leoo-c1/FPGA-Ethernet-FFT/rtl/fifo/audio_fifo_inst.v

audio_fifo	audio_fifo_inst (
	.aclr ( aclr_sig ),
	.data ( data_sig ),
	.rdclk ( rdclk_sig ),
	.rdreq ( rdreq_sig ),
	.wrclk ( wrclk_sig ),
	.wrreq ( wrreq_sig ),
	.q ( q_sig ),
	.rdempty ( rdempty_sig ),
	.rdusedw ( rdusedw_sig ),
	.wrfull ( wrfull_sig )
	);
