leoo-c1/FPGA-Ethernet-FFT/rtl/ram/amplitude_ram_inst.v

amplitude_ram	amplitude_ram_inst (
	.data ( data_sig ),
	.rdaddress ( rdaddress_sig ),
	.rdclock ( rdclock_sig ),
	.wraddress ( wraddress_sig ),
	.wrclock ( wrclock_sig ),
	.wren ( wren_sig ),
	.q ( q_sig )
	);
