leoo-c1/FPGA-Ethernet-FFT/rtl/fft/audio_fft/simulation/submodules/aldec/asj_fft_cnt_ctrl.vhd

-- (C) 2001-2025 Altera Corporation. All rights reserved.
-- This simulation model contains highly confidential and
-- proprietary information of Altera and is being provided
-- in accordance with and subject to the protections of the
-- applicable Altera Program License Subscription Agreement
-- which governs its use and disclosure. Your use of Altera
-- Corporation's design tools, logic functions and other
-- software and tools, and its AMPP partner logic functions,
-- and any output files from any of the foregoing (including device
-- programming or simulation files), and any associated
-- documentation or information are expressly subject to the
-- terms and conditions of the Altera Program License Subscription
-- Agreement, Altera IP License Agreement, or other
-- applicable license agreement, including, without limitation,
-- that your use is for the sole purpose of simulating designs
-- for use exclusively in logic devices manufactured by Altera and sold
-- by Altera or its authorized distributors. Please refer to the
-- applicable agreement for further details. Altera products and
-- services are protected under numerous U.S. and foreign patents,
-- maskwork rights, copyrights and other intellectual property laws.
-- Altera assumes no responsibility or liability arising out of the
-- application or use of this simulation model.
-- ACDS 25.1
`protect begin_protected
`protect version = 1
`protect encrypt_agent= "Aldec protectip", encrypt_agent_info= "Riviera-PRO 2019.10.138"
`protect key_keyowner= "Aldec", key_keyname= "ALDEC15_001", key_method= "rsa"
`protect encoding= (enctype="base64", line_length= 76, bytes= 256)
`protect key_block
D6r/H3scLRJbsmm2tHHAxXEU+LshsgGUUxx6U/Av3nT5sLwHCaNXLklHGkLletBJadBOJ52HiAVb
UNIvA2nUEzizdXMaJw2Dnt8pJjICWeT8NKfpqt9C8ROTuswHr4uVa/bZ/E3zMZ9jrEOYS0w/Dkw4
8y2Y6R2EKdo0C9tKc41cyNREAT+XVDKpEQyvu8E1VtJbTj6pT3H6SwwOo2JiY+xH8685eJ3sPCNR
PHIQPUK+86oMRdzpa3lwHQ1bov0JI3x8/ro1ZtiMw7tek+kP83v+5oLomvXD3rV+YauWSvqCHI5g
DUxbj6OMxBiYSeZxZS8LhIv59MJjiUg+RFlcag==
`protect data_keyowner= "altera", data_keyname= "altera"
`protect data_method= "aes128-cbc"
`protect encoding= (enctype="base64", line_length= 76, bytes= 7712)
`protect data_block
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
+EMPGUcuEIcewkYXFa5RcwA=
`protect end_protected
