leoo-c1/FPGA-Ethernet-FFT/rtl/fft/audio_fft/simulation/submodules/aldec/asj_fft_cnt_ctrl_de.vhd

-- (C) 2001-2025 Altera Corporation. All rights reserved.
-- This simulation model contains highly confidential and
-- proprietary information of Altera and is being provided
-- in accordance with and subject to the protections of the
-- applicable Altera Program License Subscription Agreement
-- which governs its use and disclosure. Your use of Altera
-- Corporation's design tools, logic functions and other
-- software and tools, and its AMPP partner logic functions,
-- and any output files from any of the foregoing (including device
-- programming or simulation files), and any associated
-- documentation or information are expressly subject to the
-- terms and conditions of the Altera Program License Subscription
-- Agreement, Altera IP License Agreement, or other
-- applicable license agreement, including, without limitation,
-- that your use is for the sole purpose of simulating designs
-- for use exclusively in logic devices manufactured by Altera and sold
-- by Altera or its authorized distributors. Please refer to the
-- applicable agreement for further details. Altera products and
-- services are protected under numerous U.S. and foreign patents,
-- maskwork rights, copyrights and other intellectual property laws.
-- Altera assumes no responsibility or liability arising out of the
-- application or use of this simulation model.
-- ACDS 25.1
`protect begin_protected
`protect version = 1
`protect encrypt_agent= "Aldec protectip", encrypt_agent_info= "Riviera-PRO 2019.10.138"
`protect key_keyowner= "Aldec", key_keyname= "ALDEC15_001", key_method= "rsa"
`protect encoding= (enctype="base64", line_length= 76, bytes= 256)
`protect key_block
hl7ze1KK95uuZX93cig8C/99H+Y/jvTrecWtORqdwT4BKLuZugFvYNe3gDdq4NNyUCLjNWNfN4v0
huzCSSlt/gMk/lz8mX791y8mMCfEYzl/dybSCZJ1gMarY0dAs6ICc0IsR/XYYPNTDvBBsqX6oz1v
cdgS4IqDEp0FLvy0f4MSXRirhCLiyGjIIBhtEK0C0z4jjtGyBcnzh3PDRIaStgAdvvy+04+DwvDk
3f2svdlKT9OBEnVwAUPbQsvOP4blE37W40UmOaBkJ1VQj56L+mOKybYgMoo0Jn43fZ9HNsaBrFhQ
djyykrSsOYpxD35mJn6XZf6n57RK4l1Gs7nC8g==
`protect data_keyowner= "altera", data_keyname= "altera"
`protect data_method= "aes128-cbc"
`protect encoding= (enctype="base64", line_length= 76, bytes= 9728)
`protect data_block
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
`protect end_protected
