leoo-c1/FPGA-Ethernet-FFT/rtl/fft/audio_fft/simulation/submodules/aldec/asj_fft_unbburst_ctrl.vhd

-- (C) 2001-2025 Altera Corporation. All rights reserved.
-- This simulation model contains highly confidential and
-- proprietary information of Altera and is being provided
-- in accordance with and subject to the protections of the
-- applicable Altera Program License Subscription Agreement
-- which governs its use and disclosure. Your use of Altera
-- Corporation's design tools, logic functions and other
-- software and tools, and its AMPP partner logic functions,
-- and any output files from any of the foregoing (including device
-- programming or simulation files), and any associated
-- documentation or information are expressly subject to the
-- terms and conditions of the Altera Program License Subscription
-- Agreement, Altera IP License Agreement, or other
-- applicable license agreement, including, without limitation,
-- that your use is for the sole purpose of simulating designs
-- for use exclusively in logic devices manufactured by Altera and sold
-- by Altera or its authorized distributors. Please refer to the
-- applicable agreement for further details. Altera products and
-- services are protected under numerous U.S. and foreign patents,
-- maskwork rights, copyrights and other intellectual property laws.
-- Altera assumes no responsibility or liability arising out of the
-- application or use of this simulation model.
-- ACDS 25.1
`protect begin_protected
`protect version = 1
`protect encrypt_agent= "Aldec protectip", encrypt_agent_info= "Riviera-PRO 2019.10.138"
`protect key_keyowner= "Aldec", key_keyname= "ALDEC15_001", key_method= "rsa"
`protect encoding= (enctype="base64", line_length= 76, bytes= 256)
`protect key_block
HGSbY7AIDmN4nCf4HE8M9eleI/NEhgI0glThhu2C2lJlaqHh7NiA3cjwd0qZlGjjAOCEnThJavfw
Ue+t2vOyKYkeIgB8p8hVF02yqVwJz/Xopbrk2M8IInKCNL+hQ4mjSnpJ5P55DhkBvHb76lSg4JIc
Pw8E1r47e+msi9+9wRgFb0o0CFG8lErPvnFh60HLuQwvHt5/9n7o4iks6TcSYWzUeDgBy4y0CRIF
tzlfctOruojg6cDcirLeOg6YqEhwDQRIxqisOvzwz/KIaaA4il/BgJl1qrA4y83CnUL2vJ+lIewh
XC/qzZB9Xw/L4bYLm1OZam4bfRekaVefYynFdw==
`protect data_keyowner= "altera", data_keyname= "altera"
`protect data_method= "aes128-cbc"
`protect encoding= (enctype="base64", line_length= 76, bytes= 6256)
`protect data_block
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
`protect end_protected
